Hugondon/STetris32/STetris32/STetris32/Core/Src/sound.c

/*
 * sound.c
 *
 *  Created on: May 2, 2021
 *      Author: hugon
 */

#include "sound.h"
#include <stdint.h>
#include <stddef.h>

uint16_t psc_array[] = {424, 403, 291, 211, 266, 232, 285, 289, 212, 195, 197, 137, 149, 136, 114, 193, 108, 113, 100, 84, 101, 81, 112, 137, 65, 68,
57, 81, 53, 64, 44, 42, 113, 81, 56, 34, 119, 34, 52, 77, 53, 32, 22, 21, 26, 21, 28, 17, 41, 17, 26, 77, 14, 16, 11, 14, 13, 21, 14, 9, 11, 9, 13, 10, 7, 8, 6, 7, 7, 6, 7, 5, 4};
uint16_t arr_array[] = {577, 573, 749, 975, 730, 790, 607, 565, 727, 746, 697, 946, 821, 849, 956, 533, 899, 811, 865, 972, 763, 898, 613, 473, 941, 849, 956, 635, 916, 716, 983, 972, 341, 449, 613, 953, 257, 849, 524, 334, 458, 716, 983, 972, 741, 866, 613, 953, 373, 849, 524, 167, 867, 716, 983, 729, 741, 433, 613, 900, 695, 802, 524, 643, 867, 716, 901, 729, 688, 758, 613, 810, 956};
uint8_t array_index = 0;


const uint8_t melody[] = {
  NOTE_E5, NOTE_E3, NOTE_B4, NOTE_C5, NOTE_D5, NOTE_E5, NOTE_D5, NOTE_C5,
  NOTE_B4, NOTE_A4, NOTE_A3, NOTE_A4, NOTE_C5, NOTE_E5, NOTE_A3, NOTE_D5,
  NOTE_C5, NOTE_B4, NOTE_E4, NOTE_G4, NOTE_C5, NOTE_D5, NOTE_E3, NOTE_E5,
  NOTE_E3, NOTE_C5, NOTE_A3, NOTE_A4, NOTE_A3, NOTE_A4, NOTE_A3, NOTE_B2,
  NOTE_C3, NOTE_D3, NOTE_D5, NOTE_F5, NOTE_A5, NOTE_C5, NOTE_C5, NOTE_G5,
  NOTE_F5, NOTE_E5, NOTE_C3, 0, NOTE_C5, NOTE_E5, NOTE_A4, NOTE_G4, NOTE_D5,
  NOTE_C5, NOTE_B4, NOTE_E4, NOTE_B4, NOTE_C5, NOTE_D5, NOTE_G4, NOTE_E5,
  NOTE_G4, NOTE_C5, NOTE_E4, NOTE_A4, NOTE_E3, NOTE_A4, 0,
  NOTE_E5, NOTE_E3, NOTE_B4, NOTE_C5, NOTE_D5, NOTE_E5, NOTE_D5, NOTE_C5,
  NOTE_B4, NOTE_A4, NOTE_A3, NOTE_A4, NOTE_C5, NOTE_E5, NOTE_A3, NOTE_D5,
  NOTE_C5, NOTE_B4, NOTE_E4, NOTE_G4, NOTE_C5, NOTE_D5, NOTE_E3, NOTE_E5,
  NOTE_E3, NOTE_C5, NOTE_A3, NOTE_A4, NOTE_A3, NOTE_A4, NOTE_A3, NOTE_B2,
  NOTE_C3, NOTE_D3, NOTE_D5, NOTE_F5, NOTE_A5, NOTE_C5, NOTE_C5, NOTE_G5,
  NOTE_F5, NOTE_E5, NOTE_C3, 0, NOTE_C5, NOTE_E5, NOTE_A4, NOTE_G4, NOTE_D5,
  NOTE_C5, NOTE_B4, NOTE_E4, NOTE_B4, NOTE_C5, NOTE_D5, NOTE_G4, NOTE_E5,
  NOTE_G4, NOTE_C5, NOTE_E4, NOTE_A4, NOTE_E3, NOTE_A4, 0,
  NOTE_E4, NOTE_E3, NOTE_A2, NOTE_E3, NOTE_C4, NOTE_E3, NOTE_A2, NOTE_E3,
  NOTE_D4, NOTE_E3, NOTE_GS2, NOTE_E3, NOTE_B3, NOTE_E3, NOTE_GS2, NOTE_E3,
  NOTE_C4, NOTE_E3, NOTE_A2, NOTE_E3, NOTE_A3, NOTE_E3, NOTE_A2, NOTE_E3,
  NOTE_GS3, NOTE_E3, NOTE_GS2, NOTE_E3, NOTE_B3, NOTE_E3, NOTE_GS2, NOTE_E3,
  NOTE_E4, NOTE_E3, NOTE_A2, NOTE_E3, NOTE_C4, NOTE_E3, NOTE_A2, NOTE_E3,
  NOTE_D4, NOTE_E3, NOTE_GS2, NOTE_E3, NOTE_B3, NOTE_E3, NOTE_GS2, NOTE_E3,
  NOTE_C4, NOTE_E3, NOTE_E4, NOTE_E3, NOTE_A4, NOTE_E3, NOTE_A2, NOTE_E3,
  NOTE_GS4, NOTE_E3, NOTE_GS2, NOTE_E3, NOTE_GS2, NOTE_E3, NOTE_GS2, NOTE_E3,
  NOTE_E5, NOTE_E3, NOTE_B4, NOTE_C5, NOTE_D5, NOTE_E5, NOTE_D5, NOTE_C5,
  NOTE_B4, NOTE_A4, NOTE_A3, NOTE_A4, NOTE_C5, NOTE_E5, NOTE_A3, NOTE_D5,
  NOTE_C5, NOTE_B4, NOTE_E4, NOTE_G4, NOTE_C5, NOTE_D5, NOTE_E3, NOTE_E5,
  NOTE_E3, NOTE_C5, NOTE_A3, NOTE_A4, NOTE_A3, NOTE_A4, NOTE_A3, NOTE_B2,
  NOTE_C3, NOTE_D3, NOTE_D5, NOTE_F5, NOTE_A5, NOTE_C5, NOTE_C5, NOTE_G5,
  NOTE_F5, NOTE_E5, NOTE_C3, 0, NOTE_C5, NOTE_E5, NOTE_A4, NOTE_G4, NOTE_D5,
  NOTE_C5, NOTE_B4, NOTE_E4, NOTE_B4, NOTE_C5, NOTE_D5, NOTE_G4, NOTE_E5,
  NOTE_G4, NOTE_C5, NOTE_E4, NOTE_A4, NOTE_E3, NOTE_A4, 0,
  NOTE_E5, NOTE_E3, NOTE_B4, NOTE_C5, NOTE_D5, NOTE_E5, NOTE_D5, NOTE_C5,
  NOTE_B4, NOTE_A4, NOTE_A3, NOTE_A4, NOTE_C5, NOTE_E5, NOTE_A3, NOTE_D5,
  NOTE_C5, NOTE_B4, NOTE_E4, NOTE_G4, NOTE_C5, NOTE_D5, NOTE_E3, NOTE_E5,
  NOTE_E3, NOTE_C5, NOTE_A3, NOTE_A4, NOTE_A3, NOTE_A4, NOTE_A3, NOTE_B2,
  NOTE_C3, NOTE_D3, NOTE_D5, NOTE_F5, NOTE_A5, NOTE_C5, NOTE_C5, NOTE_G5,
  NOTE_F5, NOTE_E5, NOTE_C3, 0, NOTE_C5, NOTE_E5, NOTE_A4, NOTE_G4, NOTE_D5,
  NOTE_C5, NOTE_B4, NOTE_E4, NOTE_B4, NOTE_C5, NOTE_D5, NOTE_G4, NOTE_E5,
  NOTE_G4, NOTE_C5, NOTE_E4, NOTE_A4, NOTE_E3, NOTE_A4, 0,
  NOTE_E4, NOTE_E3, NOTE_A2, NOTE_E3, NOTE_C4, NOTE_E3, NOTE_A2, NOTE_E3,
  NOTE_D4, NOTE_E3, NOTE_GS2, NOTE_E3, NOTE_B3, NOTE_E3, NOTE_GS2, NOTE_E3,
  NOTE_C4, NOTE_E3, NOTE_A2, NOTE_E3, NOTE_A3, NOTE_E3, NOTE_A2, NOTE_E3,
  NOTE_GS3, NOTE_E3, NOTE_GS2, NOTE_E3, NOTE_B3, NOTE_E3, NOTE_GS2, NOTE_E3,
  NOTE_E4, NOTE_E3, NOTE_A2, NOTE_E3, NOTE_C4, NOTE_E3, NOTE_A2, NOTE_E3,
  NOTE_D4, NOTE_E3, NOTE_GS2, NOTE_E3, NOTE_B3, NOTE_E3, NOTE_GS2, NOTE_E3,
  NOTE_C4, NOTE_E3, NOTE_E4, NOTE_E3, NOTE_A4, NOTE_E3, NOTE_A2, NOTE_E3,
  NOTE_GS4, NOTE_E3, NOTE_GS2, NOTE_E3, NOTE_GS2, NOTE_E3, NOTE_GS2, NOTE_E3,
};

// https://www.microchip.com/forums/m57199.aspx
const size_t sizeof_melody = sizeof(melody);

const uint8_t noteDurations[] = {
  8,8,8,8,8,16,16,8,8,8,8,8,8,8,8,8,8,8,8,8,8,8,8,8,8,8,8,8,8,8,8,8,8,
  8,4,8,8,16,16,8,8,8,8,8,8,8,16,16,8,8,8,8,8,8,8,8,8,8,8,8,8,8,4,4,
  8,8,8,8,8,16,16,8,8,8,8,8,8,8,8,8,8,8,8,8,8,8,8,8,8,8,8,8,8,8,8,8,8,
  8,4,8,8,16,16,8,8,8,8,8,8,8,16,16,8,8,8,8,8,8,8,8,8,8,8,8,8,8,4,4,
  8,8,8,8,8,8,8,8,8,8,8,8,8,8,8,8,8,8,8,8,8,8,8,8,8,8,8,8,8,8,8,8,
  8,8,8,8,8,8,8,8,8,8,8,8,8,8,8,8,8,8,8,8,8,8,8,8,8,8,8,8,8,8,8,8,
  8,8,8,8,8,16,16,8,8,8,8,8,8,8,8,8,8,8,8,8,8,8,8,8,8,8,8,8,8,8,8,8,8,
  8,4,8,8,16,16,8,8,8,8,8,8,8,16,16,8,8,8,8,8,8,8,8,8,8,8,8,8,8,4,4,
  8,8,8,8,8,16,16,8,8,8,8,8,8,8,8,8,8,8,8,8,8,8,8,8,8,8,8,8,8,8,8,8,8,
  8,4,8,8,16,16,8,8,8,8,8,8,8,16,16,8,8,8,8,8,8,8,8,8,8,8,8,8,8,4,4,
  8,8,8,8,8,8,8,8,8,8,8,8,8,8,8,8,8,8,8,8,8,8,8,8,8,8,8,8,8,8,8,8,
  8,8,8,8,8,8,8,8,8,8,8,8,8,8,8,8,8,8,8,8,8,8,8,8,8,8,8,8,8,8,8,8,
};
